slash128v6/DC33_Cnet_Badge/Docs/WIP/Images/Flashing & Configuration/IMG_2678.PNG

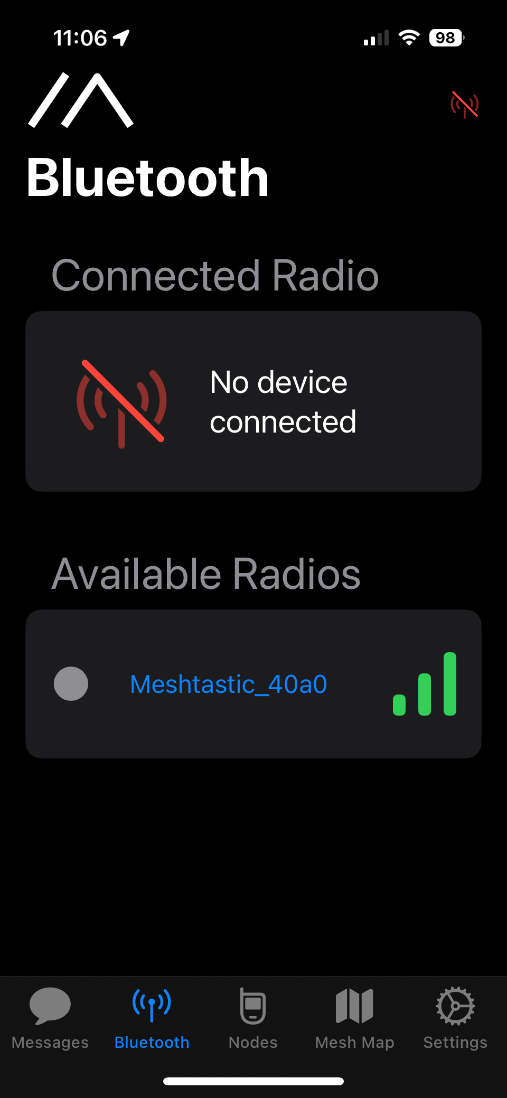
Docs/WIP/Images/Flashing & Configuration/IMG_2678.PNG
