slash128v6/DC33_Cnet_Badge/Docs/WIP/Images/Flashing & Configuration/IMG_2681.JPEG

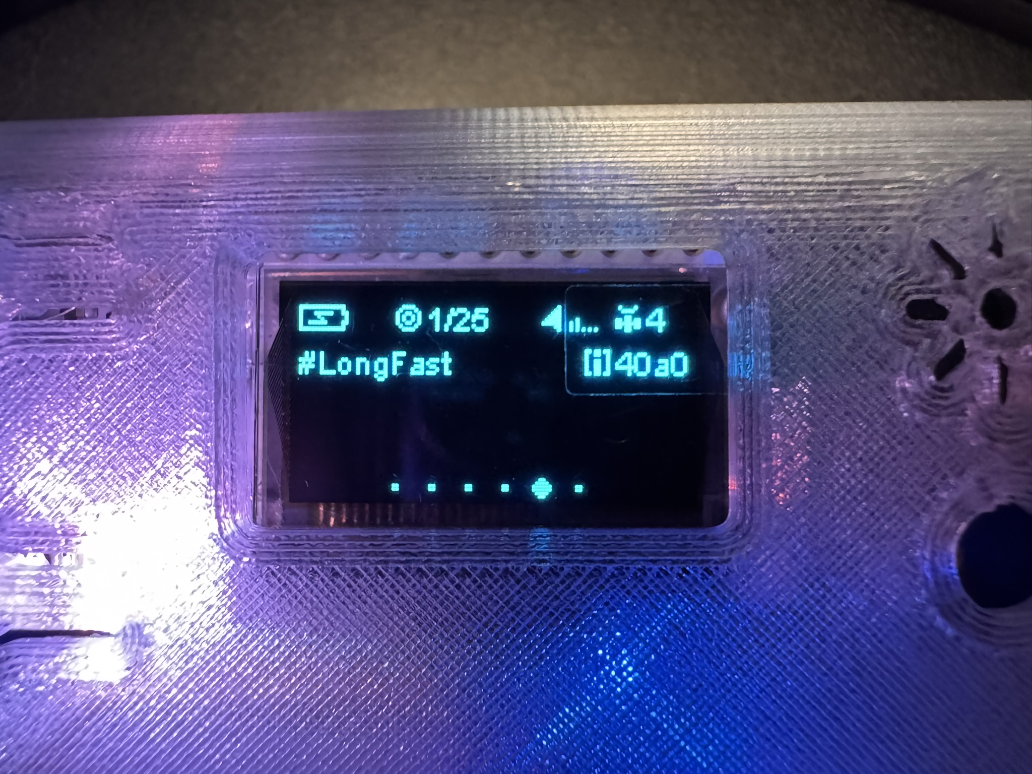
Docs/WIP/Images/Flashing & Configuration/IMG_2681.JPEG
