slash128v6/DC33_Cnet_Badge/Docs/WIP/Images/Flashing & Configuration/IMG_2685.PNG

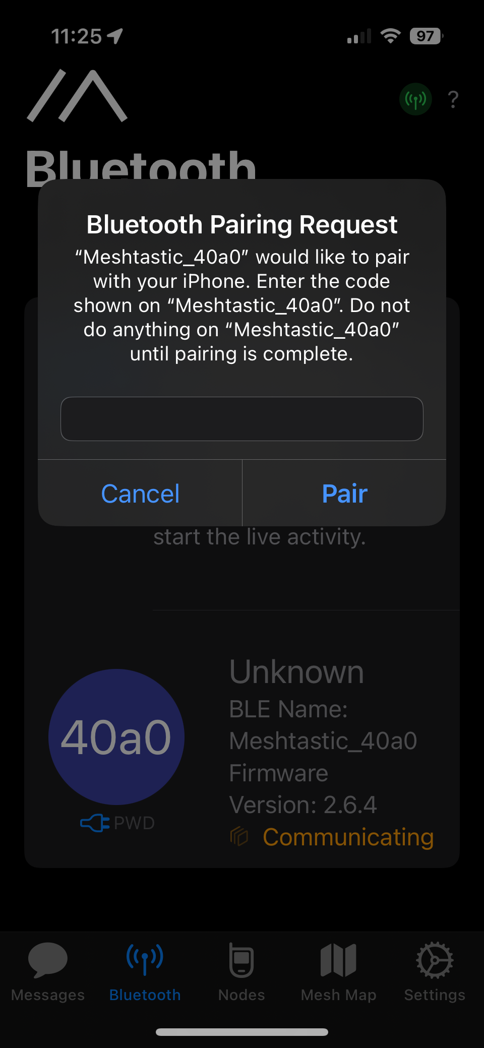
Docs/WIP/Images/Flashing & Configuration/IMG_2685.PNG
