slash128v6/DC33_Cnet_Badge/Docs/WIP/Images/Flashing & Configuration/Screenshot 2025-06-06 115823.png

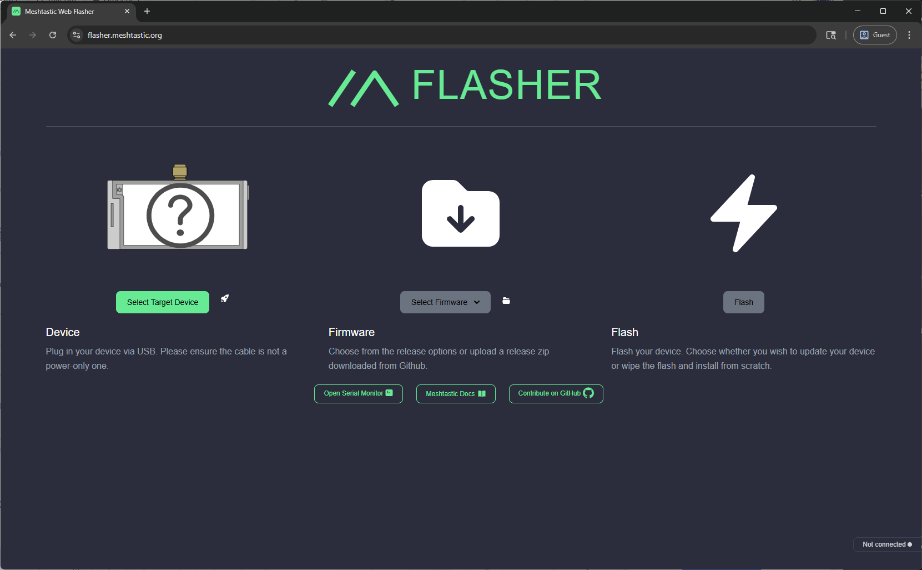
Docs/WIP/Images/Flashing & Configuration/Screenshot 2025-06-06 115823.png
