slash128v6/DC33_Cnet_Badge/Hardware/Heltec V3 LoRa/HTIT-WB32LAF_V3副本.png

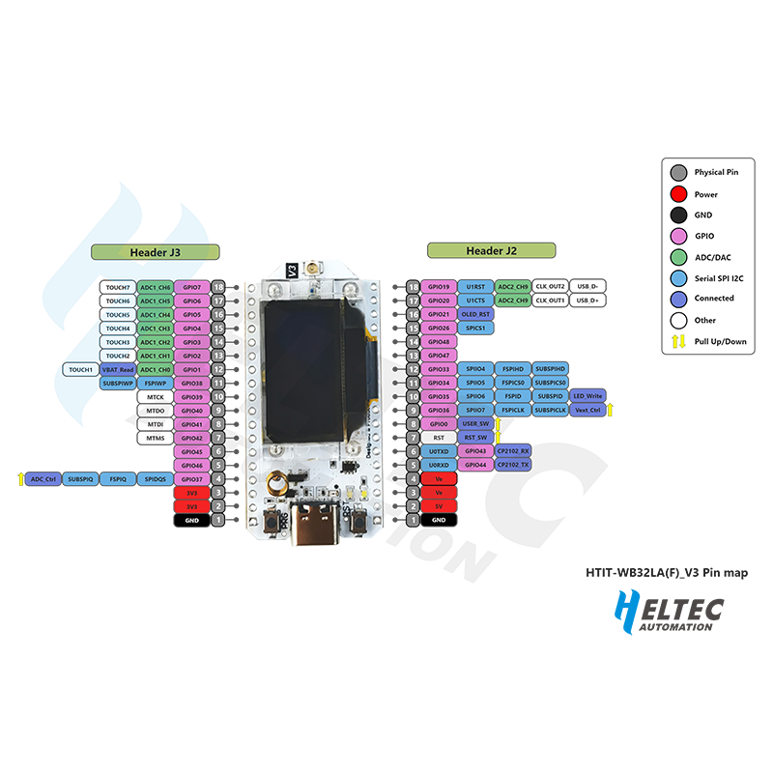
Hardware/Heltec V3 LoRa/HTIT-WB32LAF_V3副本.png
