slash128v6/DC33_Cnet_Badge/Hardware/Heltec V3 LoRa/wifi-lora-32-pin_map-1024x597.png

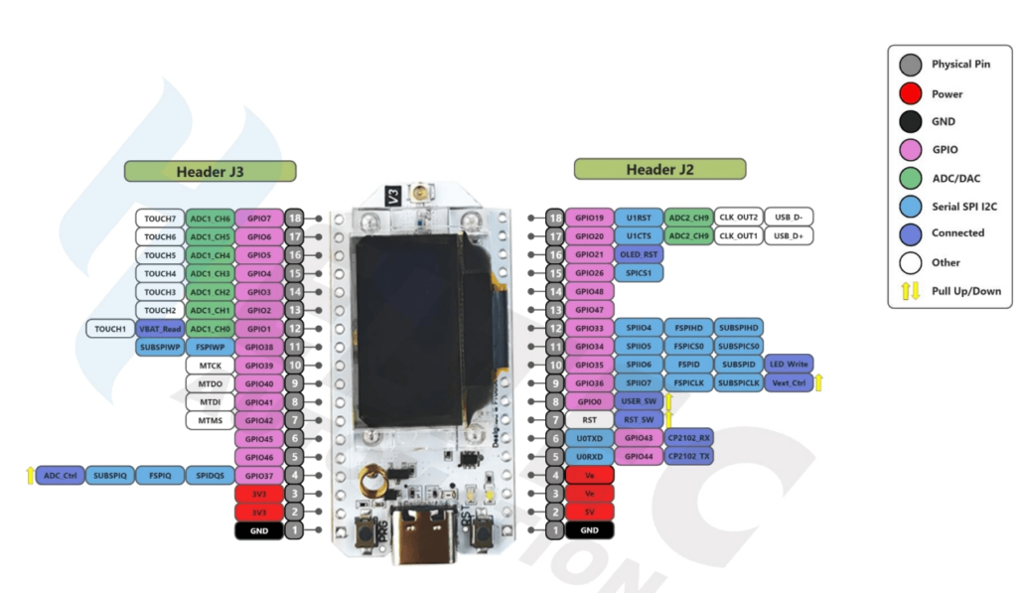
Hardware/Heltec V3 LoRa/wifi-lora-32-pin_map-1024x597.png
