slash128v6/DC33_Cnet_Badge/Hardware/3D Models/Vibra1.step

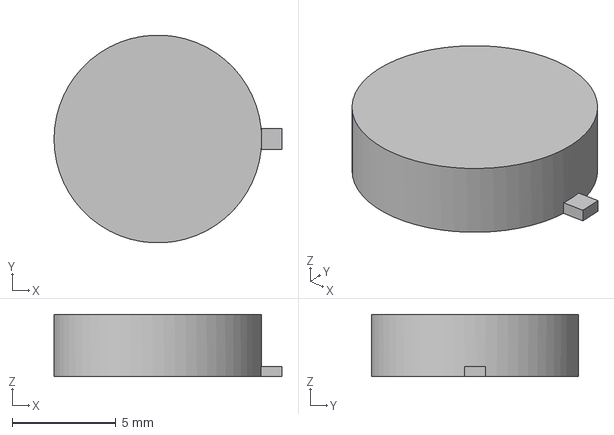
[picture p74: CAD file, 2024-12-09]
Hardware/3D Models/Vibra1.step
11.0 x 9.99 x 3.00 mm
