slash128v6/DC33_Cnet_Badge/Docs/WIP/Images/Hardware Assembly/IMG_2639.JPEG

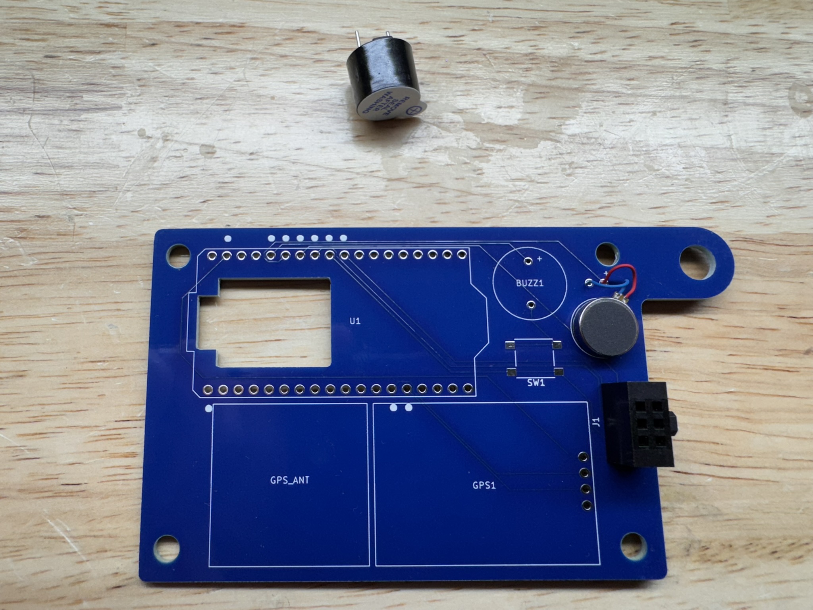
Docs/WIP/Images/Hardware Assembly/IMG_2639.JPEG
