slash128v6/DC33_Cnet_Badge/Docs/WIP/Images/Hardware Assembly/IMG_2650.JPEG

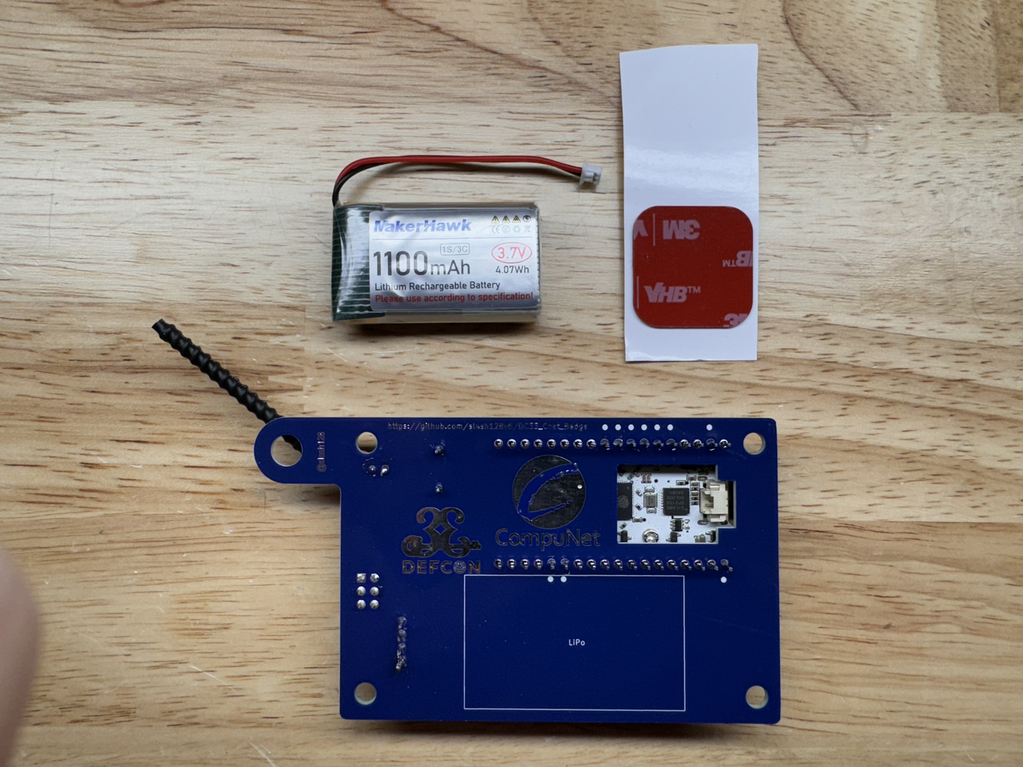
Docs/WIP/Images/Hardware Assembly/IMG_2650.JPEG
